Limx1994/esp8266-ac-thermostat/Sof/main/sleep_trace.h

#pragma once

/* 测温时调用；最多每 30 秒汇总 RAM 诊断和最近四次低层调用，不创建任务或定时器。
 * 包含 RTOS/FRC2 期限快照、RTC 编程期限和调用区间估算。
 * 汇总有限的 1 秒内任务等待和调用位置；记录不代表本次真实唤醒原因。
 * RTC 时间包含进出开销，不是精确的硬件睡眠时长；期限快照不是实际唤醒源。
 */
void sleep_trace_report(void);
